Droid-MAX/ffp/software/src/programmer.rs

use std::time::Duration;
use failure::ResultExt;
use crate::{FFPError, Result};

#[derive(Copy, Clone, Debug)]
#[repr(u8)]
enum Command {
    SetCS = 1,
    SetFPGAReset = 2,
    SetMode = 3,
    SetTPwr = 4,
    SetLED = 6,
    Bootload = 7,
}

#[derive(Copy, Clone, Debug)]
#[repr(u16)]
enum Mode {
    HighZ = 0,
    Flash = 1,
    FPGA = 2,
}

/// Interface to FFP hardware
pub struct Programmer<'a> {
    handle: libusb::DeviceHandle<'a>,
}

impl <'a> Programmer<'a> {
    const ID_VENDOR: u16        = 0x1209;
    const ID_PRODUCT: u16       = 0xff50;
    const REQUEST_TYPE_SET: u8  = 2 << 5;
    const TX_EP: u8             = 0x01;
    const RX_EP: u8             = 0x81;
    const CHUNK_SIZE: usize     = 64;

    /// Create a new `Programmer` using the provided `DeviceHandle`.
    ///
    /// Turns on the FFP LED.
    pub fn from_handle(mut handle: libusb::DeviceHandle<'a>) -> Result<Self> {
        handle.claim_interface(0).context("Error claiming interface")?;
        let programmer = Self { handle };
        programmer.led_on()?;
        Ok(programmer)
    }

    /// Get a list of all attached FFP serial numbers
    pub fn get_serials(context: &'a libusb::Context) -> Result<Vec<String>> {
        let devices = Self::enumerate_devices(context)?;
        Ok(devices.iter().map(|(_, serial)| serial.clone()).collect())
    }

    /// Create a new `Programmer` by finding an attached FFP on the USB bus
    pub fn find(context: &'a libusb::Context) -> Result<Self> {
        let devices = Self::enumerate_devices(context)?;
        match devices.len() {
            0 => Err(FFPError::NoDeviceFound)?,
            1 => {
                let handle = devices[0].0.open().context("Error opening device")?;
                Self::from_handle(handle)
            },
            _ => {
                println!("Multiple FFP devices found:");
                for (idx, (_, serial)) in devices.iter().enumerate() {
                    println!("    {}: {}", idx, serial);
                }
                Err(FFPError::MultipleDevicesFound)?
            }
        }
    }

    /// Create a new `Programmer` by finding the specific FFP with given serial number
    pub fn by_serial(context: &'a libusb::Context, serial: &str) -> Result<Self> {
        let devices = Self::enumerate_devices(context)?;
        for (device, device_serial) in devices {
            if device_serial == serial {
                let handle = device.open().context("Error opening device")?;
                return Self::from_handle(handle);
            }
        }
        Err(FFPError::DeviceNotFound)?
    }

    /// Create a new `Programmer` by indexing the list of all found FFP devices
    pub fn by_index(context: &'a libusb::Context, index: usize) -> Result<Self> {
        let devices = Self::enumerate_devices(context)?;
        if index < devices.len() {
            let handle = devices[index].0.open().context("Error opening device")?;
            Self::from_handle(handle)
        } else {
            Err(FFPError::DeviceNotFound)?
        }
    }

    /// Turn on the FFP LED
    pub fn led_on(&self) -> Result<()> {
        self.set(Command::SetLED, 1)
    }

    /// Turn off the FFP LED
    pub fn led_off(&self) -> Result<()> {
        self.set(Command::SetLED, 0)
    }

    /// Assert the FPGA reset signal
    pub fn reset(&self) -> Result<()> {
        self.set(Command::SetFPGAReset, 0)
    }

    /// Deassert the FPGA reset signal
    pub fn unreset(&self) -> Result<()> {
        self.set(Command::SetFPGAReset, 1)
    }

    /// Assert SPI CS
    pub fn select(&self) -> Result<()> {
        self.set(Command::SetCS, 0)
    }

    /// Deassert SPI CS
    pub fn unselect(&self) -> Result<()> {
        self.set(Command::SetCS, 1)
    }

    /// Set SPI pins to high impedance
    pub fn high_z_mode(&self) -> Result<()> {
        self.set(Command::SetMode, Mode::HighZ as u16)
    }

    /// Set SPI pins to flash mode (for communicating with SPI flash)
    pub fn flash_mode(&self) -> Result<()> {
        self.set(Command::SetMode, Mode::Flash as u16)
    }

    /// Set SPI pins to fpga mode (for communicating with FPGA)
    pub fn fpga_mode(&self) -> Result<()> {
        self.set(Command::SetMode, Mode::FPGA as u16)
    }

    /// Enable target power switch on FFP
    pub fn power_on(&self) -> Result<()> {
        self.set(Command::SetTPwr, 1)
    }

    /// Disable target power switch on FFP
    pub fn power_off(&self) -> Result<()> {
        self.set(Command::SetTPwr, 0)
    }

    /// Reset FFP hardware into USB bootloader mode
    pub fn bootload(&self) -> Result<()> {
        self.set(Command::Bootload, 0)
    }

    /// Write `data` to the FFP's bulk data endpoint
    pub fn write(&self, data: &[u8]) -> Result<Vec<u8>> {
        let timeout = Duration::from_millis(100);
        let mut rx = Vec::new();
        for chunk in data.chunks(Self::CHUNK_SIZE) {
            let mut rx_chunk = vec![0u8; chunk.len()];
            self.handle.write_bulk(Self::TX_EP, chunk, timeout)
                       .context("Error writing data")?;
            match self.handle.read_bulk(Self::RX_EP, &mut rx_chunk, timeout) {
                Ok(n) if n == chunk.len() => rx.extend(rx_chunk),
                Ok(n) => Err(FFPError::NotEnoughData {
                    expected: chunk.len(), read: n
                })?,
                Err(e) => Err(FFPError::USBError(e))
                          .context("Error reading data")?,
            }
        }
        Ok(rx)
    }

    /// Issue a control request to a specific value
    fn set(&self, request: Command, value: u16) -> Result<()> {
        let timeout = Duration::from_millis(100);
        match self.handle.write_control(
            Self::REQUEST_TYPE_SET, request as u8, value, 0, &[], timeout)
        {
            Ok(_) => Ok(()),
            Err(e) => Err(FFPError::USBError(e))
                        .context(format!("Error sending request {:?} {}", request, value))?,
        }
    }

    /// Return a list of all discovered FFP devices (by vendor and product ID)
    fn enumerate_devices(context: &'a libusb::Context) -> Result<Vec<(libusb::Device, String)>> {
        let timeout = Duration::from_millis(100);
        let mut devices = Vec::new();
        for device in context.devices().context("Error getting devices")?.iter() {
            let dd = device.device_descriptor().context("Error reading descriptor")?;
            if dd.vendor_id() == Self::ID_VENDOR && dd.product_id() == Self::ID_PRODUCT {
                let handle = device.open().context("Error opening device")?;
                let languages = handle.read_languages(timeout)?;
                let serial = handle.read_serial_number_string(languages[0], &dd, timeout)?;
                devices.push((device, serial));
            }
        }
        Ok(devices)
    }
}

impl<'a> Drop for Programmer<'a> {
    /// When dropped, go to high-z mode and turn off the FFP LED
    fn drop(&mut self) {
        self.high_z_mode().ok();
        self.led_off().ok();
    }
}
